LESA-RPI/LESA_OccupancyUnit/Hardware/Enclosure/RenderImages/OSCASSY1.png

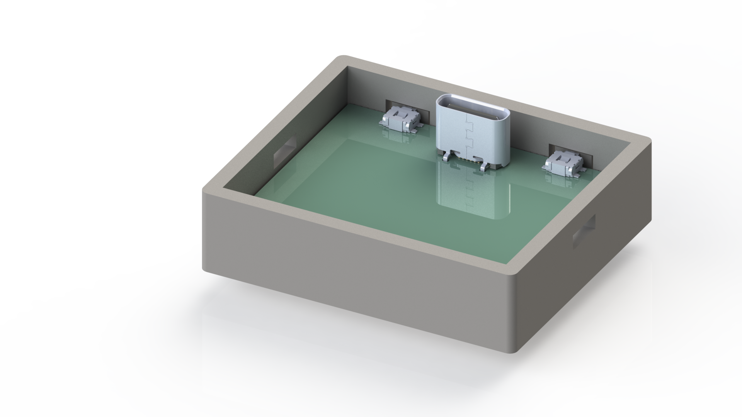
Hardware/Enclosure/RenderImages/OSCASSY1.png
