LESA-RPI/LESA_OccupancyUnit/Hardware/Enclosure/RenderImages/OSCASSY2.png

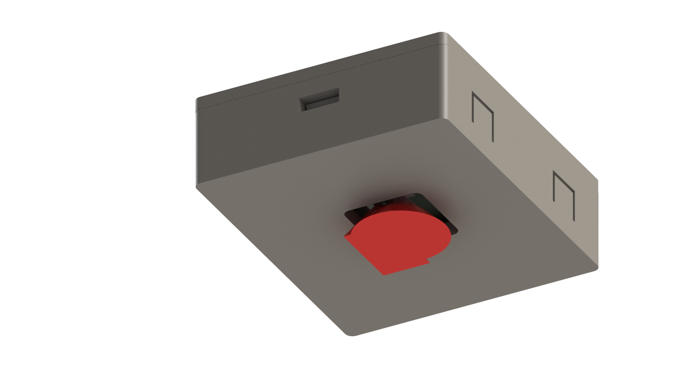
Hardware/Enclosure/RenderImages/OSCASSY2.png
