LESA-RPI/LESA_OccupancyUnit/Hardware/Enclosure/RenderImages/OSCT3view2.png

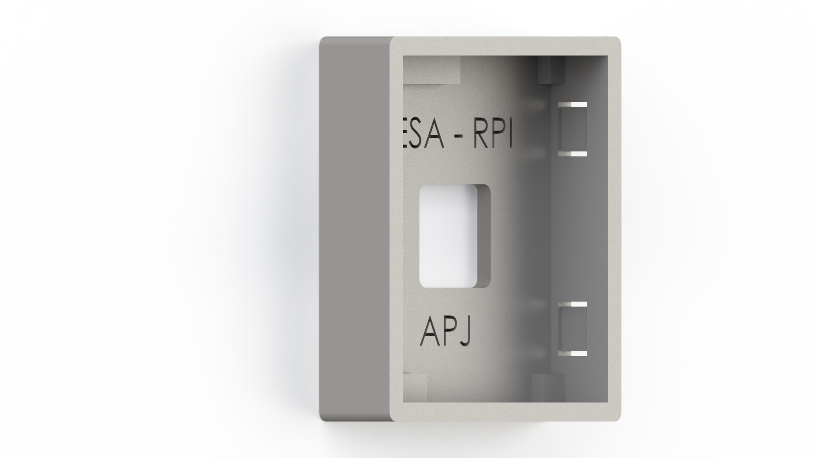
Hardware/Enclosure/RenderImages/OSCT3view2.png
