LESA-RPI/LESA_OccupancyUnit/Hardware/Enclosure/RenderImages/TCS3430.png

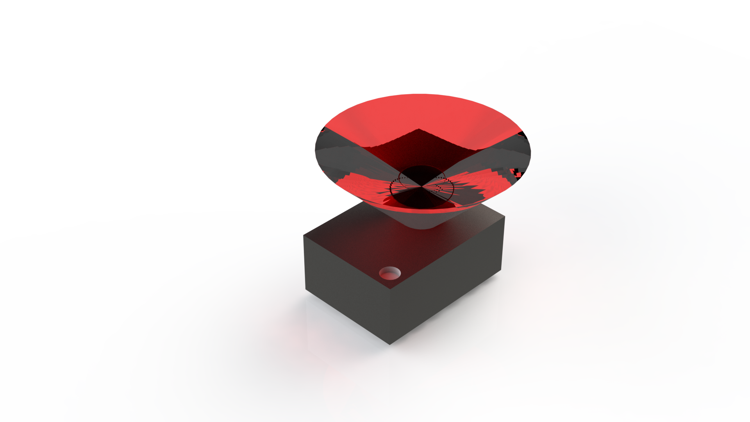
Hardware/Enclosure/RenderImages/TCS3430.png
