LESA-RPI/LESA_OccupancyUnit/Hardware/Enclosure/RenderImages/VL53L8CX.png

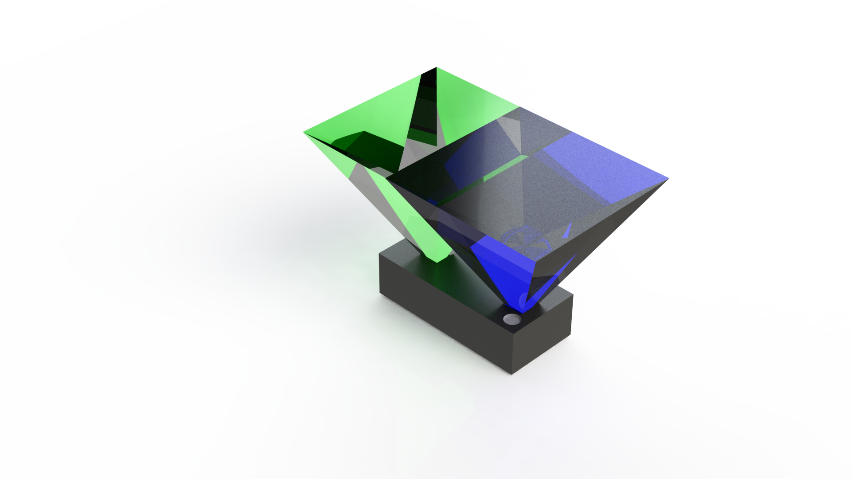
Hardware/Enclosure/RenderImages/VL53L8CX.png
