LESA-RPI/LESA_OccupancyUnit/Hardware/PCBA/-A/Occupancy_Sensor-A/Occupancy_Sensor-A.kicad_sch

## KiCad design Hardware/PCBA/-A/Occupancy_Sensor-A/Occupancy_Sensor-A.kicad_sch (2023-11-09)


Parts:
AE1: Antenna; AN3359_Meander_Antenna
C1, C13, C15, C19: 4.7u; C_0402_1005Metric; Part # CL05A475MP5NRNC
C2, C4, C9, C16, C17, C18, C20, C21, C22: 100n; C_0402_1005Metric; Part # CL05A104KA5NNNC
C3, C5, C6, C7, C8, C10: 1u; C_0402_1005Metric; Part # CL05A105KP5NNNC
C11, C26: 10n; C_0402_1005Metric; Part # CL05B103KB5NNNC
C12, C14: 10p; C_0402_1005Metric; Part # GRM1555C1H100FA01D
C23: 100p; C_0402_1005Metric; Part # GRM1555C1H101JA01D
C24: 0.8p; C_0402_1005Metric; Part # CC0402BRNPO9BNR80
C25: 0.3p; C_0402_1005Metric; Part # GRM1555C1HR30BA01J
C27, C28, C29: C_0402_1005Metric; not fitted
C30: 1.2p; C_0402_1005Metric; Part # CC0402CRNPO9BN1R2
C31: 10n; C_0402_1005Metric; Part # CL05B103KB5NNNC; not fitted
D1: PWR; LED_0603_1608Metric; Part # LTST-C191KRKT
D2: STAT; LED_0603_1608Metric; Part # LTST-C190GKT
J2: Conn_02x05_Odd_Even; PinHeader_2x05_P1.27mm_Vertical_SMD; Part # 20021121-00010C4LF
J3: Conn_Coaxial; CONUFL001-SMD-T; Part # CONUFL001-SMD-T
J4: USB_C_Receptacle; USB4120-03-C; Part # USB4115-03-C
JP1: BATT; SolderJumper-2_P1.3mm_Open_RoundedPad1.0x1.5mm
JP2: USB; SolderJumper-2_P1.3mm_Bridged_RoundedPad1.0x1.5mm
L1: 10u; L_0805_2012Metric; Part # LQM21FN100M70L
L2: 10n; L_0402_1005Metric; Part # LQG15WZ10NJ02D
L3: 2.7n; L_0402_1005Metric; Part # LQG15HS2N7S02D
L4: 0R; R_0603_1608Metric
L5: 3.6n; L_0402_1005Metric; Part # LQG15HS3N6S02
Q1, Q2, Q3, Q4, Q7: BSS138; SOT-23; Part # BSS138
Q6: DMG1012T; SOT-523; Part # DMG1012T-7
R1, R2: 5.1K; R_0402_1005Metric; Part # ERJ-2RKF5101X
R3, R5, R6, R7, R9, R10, R12: 47K; R_0402_1005Metric; Part # ERJ-2RKF4702X
R4, R11: 40.2K; R_0402_1005Metric; Part # RC0402FR-1340K2L
R8, R13, R15, R21: 1K; R_0402_1005Metric; Part # ERJ-2RKF1001X
R14, R16, R17, R18, R19, R20: 2.2K; R_0402_1005Metric; Part # ERJ-2RKF2201X
SW1: BOOT; EVQ-P7A01P; Part # EVQ-P7A01P
SW2: RST; EVQ-P7A01P; Part # EVQ-P7A01P
TP1: 5V; TestPoint_Pad_D2.0mm
TP2: GND; TestPoint_Pad_D2.0mm
TP3: SCL; TestPoint_Pad_D1.0mm
TP4: SDA; TestPoint_Pad_D1.0mm
TP5: INTT; TestPoint_Pad_D1.0mm
TP7: INTC; TestPoint_Pad_D1.0mm
U1: TPS7A0333PDBVR; SOT-23-5; Part # TPS7A0333PDBVR
U2: VL53L8CX; Part # VL53L8CXV0GC/1
U3: ECMF02-2AMX6; ST_UQFN-6L_1.5x1.7mm_P0.5mm; Part # ECMF02-2AMX6
U4: TPS7A0318PDBVR; SOT-23-5; Part # TPS7A0318PDBVR
U5: TCS3430; Part # TCS34303
U6: STM32WB55CGUx; QFN-48-1EP_7x7mm_P0.5mm_EP5.6x5.6mm; Part # STM32WB55CGU6
U8: DEA162450BT-1295A1; Part # DEA162450BT-1295A1
Y2: NX2016SA_32M; Part # CS06465-32M
Y3: NX2012_32K768; Part # MU00797-32.768K

Connections:
1V8_EN: U4.3 (EN), U6.12 (PA3)
+1V8: C2.1, C4.1, C7.1, C8.1, Q1.1 (G), Q2.1 (G), Q3.1 (G), Q4.1 (G), Q7.1 (G), R6.1, R7.1, R14.1, R16.1, R19.1, U2.A3 (IOVDD), U2.B7 (CORE_1V8), U4.5 (OUT), U5.1 (VDD)
+3.3V: C1.1, C5.1, C10.1, C11.1, C13.1, C15.1, C16.1, C17.1, C18.1, C20.1, C22.1, C23.1, J2.1, JP1.1 (A), JP2.1 (A), R9.1, R10.1, R17.1, R18.1, R20.1, R21.1, SW1.2, U1.5 (OUT), U2.C4 (AVDD), U6.8 (VDDA), U6.20 (VDD), U6.23 (VDDRF), U6.34 (VDDSMPS), U6.35 (VDD), U6.48 (VDD)
BOOT: R15.1, SW1.1, U6.4 (PH3)
GND: C1.2, C2.2, C3.2, C4.2, C5.2, C6.2, C7.2, C8.2, C9.2, C10.2, C11.2, C12.1, C13.2, C14.2, C15.2, C16.2, C17.2, C18.2, C19.2, C20.2, C21.2, C22.2, C23.2, C24.2, C25.2, C27.2, C28.2, C29.2, C30.2, D1.1 (K), D2.1 (K), J2.3, J2.5, J2.9, J3.2 (Ext), J4.A1 (GND), J4.A12 (GND), J4.B1 (GND), J4.B12 (GND), Q6.1 (G), R1.2, R2.2, R3.2, R5.2, R12.2, R15.2, SW2.2, TP2.1, U1.2 (GND), U2.A6 (RSVD1), U2.A7 (RSVD2), U2.B4 (PAD), U2.C3 (GND), U2.C6 (RSVD3), U2.C7 (GND), U3.3 (GND), U4.2 (GND), U5.7 (GND), U5.8 (GND), U6.22 (VSSRF), U6.32 (VSSSMPS), U6.49 (VSS), U8.2 (GND), U8.4 (GND), Y2.2, Y2.4
I2C_RST: R4.1, U6.17 (PA8)
I2C_RST_1V8: R4.2, R5.1, U2.C2 (NCS)
INT_CLR_1V8: Q3.2 (S), R14.2, U5.4 (INT)
INT_CLR_3V3: Q3.3 (D), R17.2, TP7.1, U6.42 (PA15)
INT_TOF_1V8: Q1.2 (S), R6.2, U2.A1 (INT)
INT_TOF_3V3: Q1.3 (D), R9.2, TP5.1, U6.15 (PA6)
LPn_1V8: R11.2, R12.1, U2.A2 (LPn)
LPn_3V3: R11.1, U6.14 (PA5)
NRST: C9.1, J2.10, R21.2, SW2.1, U6.7 (NRST)
unnamed: AE1.1, C30.1, L5.2
unnamed: C19.1, L1.1, U6.31 (VFBSMPS)
unnamed: C21.1, JP2.2 (B), U6.40 (VDDUSB)
unnamed: C25.1, L3.2, U8.1
unnamed: C26.1, C31.1, U8.3
unnamed: C26.2, C29.1, L5.1
unnamed: C27.1, J3.1 (In), L4.2
unnamed: C28.1, C31.2, L4.1
unnamed: D1.2 (A), R8.1
unnamed: D2.2 (A), R13.1
unnamed: J4.A5 (CC1), R1.1
unnamed: J4.A6 (D+), J4.B6 (D+), U3.1 (D+_in)
unnamed: J4.A7 (D-), J4.B7 (D-), U3.2 (D-_in)
unnamed: J4.B5 (CC2), R2.1
unnamed: JP1.2 (B), U6.1 (VBAT)
unnamed: L1.2, L2.1
unnamed: L2.2, U6.33 (VLXSMPS)
unnamed: Q6.2 (S), TP1.1
unnamed: R3.1, U2.C1 (SPI_I2C_N)
OSC32_IN: C14.1, U6.2 (PC14), Y3.2
OSC32_OUT: C12.2, U6.3 (PC15), Y3.1
OSC_IN: U6.25 (OSC_IN), Y2.3
OSC_OUT: U6.24 (OSC_OUT), Y2.1
PB5: R13.2, U6.45 (PB5)
RF: C24.1, L3.1, U6.21 (RF1)
SCL_1V8: Q4.2 (S), R16.2, U2.A5 (SCL/MCLK), U5.3 (SCL)
SCL_3V3: Q4.3 (D), R18.2, TP3.1, U6.46 (PB6)
SDA_1V8: Q7.2 (S), R19.2, U2.A4 (SDA/MOSI), U5.2 (SDA)
SDA_3V3: Q7.3 (D), R20.2, TP4.1, U6.47 (PB7)
SWCLK: J2.4, U6.41 (PA14)
SWDIO: J2.2, U6.39 (PA13)
SWO: J2.6, U6.43 (PB3)
SYNC_1V8: Q2.2 (S), R7.2, U2.B1 (SYNC)
SYNC_3V3: Q2.3 (D), R10.2, U6.16 (PA7)
USB_N: U3.5 (D-_out), U6.37 (PA11)
USB_P: U3.6 (D+_out), U6.38 (PA12)
VBUS: C3.1, C6.1, J4.A4 (VBUS), J4.A9 (VBUS), J4.B4 (VBUS), J4.B9 (VBUS), Q6.3 (D), R8.2, U1.1 (IN), U1.3 (EN), U4.1 (IN)

Notes on the sheet:
USB
STATUS LED
TCS340 COLOR SENSOR
Depop FET and 3V3-side pullup if SYNC not used
VL53L8 TOF SENSOR
BOOT SELECTOR
Microcontroller Flash/Ram Code: STM32WB55CxU6 Where x is: C = 256Kb E = 512Kb G = 1024Kb Consider using a lower memory microcontroller if firmware not utilizing excess flash.
REGULATORS
Antenna Band Filter
SWD HEADER
I2C Reset active high Voltage divider ensures 1.8V and required 47K pulldown
RESET SWITCH
MICROCONTROLLER
