LESA-RPI/LESA_OccupancyUnit/Core/Inc/main.h

#define B1_Pin GPIO_PIN_4
#define B1_GPIO_Port GPIOC
#define LD2_Pin GPIO_PIN_0
#define LD2_GPIO_Port GPIOB
#define LD3_Pin GPIO_PIN_1
#define LD3_GPIO_Port GPIOB
#define JTMS_Pin GPIO_PIN_13
#define JTMS_GPIO_Port GPIOA
#define JTCK_Pin GPIO_PIN_14
#define JTCK_GPIO_Port GPIOA
#define B2_Pin GPIO_PIN_0
#define B2_GPIO_Port GPIOD
#define B3_Pin GPIO_PIN_1
#define B3_GPIO_Port GPIOD
#define C_Pin GPIO_PIN_2
#define C_GPIO_Port GPIOC
#define JTDO_Pin GPIO_PIN_3
#define JTDO_GPIO_Port GPIOB
#define LD1_Pin GPIO_PIN_5
#define LD1_GPIO_Port GPIOB
#define STLINK_RX_Pin GPIO_PIN_6
#define STLINK_RX_GPIO_Port GPIOB
#define STLINK_TX_Pin GPIO_PIN_7
#define STLINK_TX_GPIO_Port GPIOB
