LESA-RPI/LESA_OccupancyUnit/CG_chip_ioc/Occ_sensor/Core/Inc/custom_ranging_sensor.h

/**
  ******************************************************************************
  * @file    custom_ranging_sensor.h
  * @author  IMG SW Application Team
  * @brief   This file contains definitions for the BSP Ranging Sensors
  *          interface for custom boards
  ******************************************************************************
  * @attention
  *
  * Copyright (c) 2022 STMicroelectronics.
  * All rights reserved.
  *
  * This software is licensed under terms that can be found in the LICENSE file
  * in the root directory of this software component.
  * If no LICENSE file comes with this software, it is provided AS-IS.
  *
  ******************************************************************************
  */

/* Define to prevent recursive inclusion -------------------------------------*/
#ifndef __CUSTOM_RANGING_SENSOR_H__
#define __CUSTOM_RANGING_SENSOR_H__

#ifdef __cplusplus
 extern "C" {
#endif

/* Includes ------------------------------------------------------------------*/

#include "custom_tof_conf.h"
#include "ranging_sensor.h"

#ifndef USE_CUSTOM_RANGING_VL53L8CX
#define USE_CUSTOM_RANGING_VL53L8CX (1U)
#endif

#if (USE_CUSTOM_RANGING_VL53L8CX == 1U)
#include "vl53l8cx.h"
#endif

#if (USE_CUSTOM_RANGING_VL53L8CX == 1U)
#define CUSTOM_VL53L8CX (0)
#endif

#define RANGING_SENSOR_VL53L8CX_ADDRESS     (VL53L8CX_DEVICE_ADDRESS)
#define RANGING_SENSOR_NB_TARGET_PER_ZONE   (VL53L8CX_NB_TARGET_PER_ZONE)
#define RANGING_SENSOR_MAX_NB_ZONES         (VL53L8CX_MAX_NB_ZONES)

#define RS_PROFILE_4x4_CONTINUOUS          (VL53L8CX_PROFILE_4x4_CONTINUOUS)
#define RS_PROFILE_4x4_AUTONOMOUS          (VL53L8CX_PROFILE_4x4_AUTONOMOUS)
#define RS_PROFILE_8x8_CONTINUOUS          (VL53L8CX_PROFILE_8x8_CONTINUOUS)
#define RS_PROFILE_8x8_AUTONOMOUS          (VL53L8CX_PROFILE_8x8_AUTONOMOUS)

#define RS_IT_DEFAULT        (VL53L8CX_IT_DEFAULT)       /*!< IT if new measurement is ready (no thresholds) */
#define RS_IT_IN_WINDOW      (VL53L8CX_IT_IN_WINDOW)     /*!< IT if distance > thresh_high */
#define RS_IT_OUT_OF_WINDOW  (VL53L8CX_IT_OUT_OF_WINDOW) /*!< IT if distance < LowThreshold OR distance > HighThreshold */
#define RS_IT_BELOW_LOW      (VL53L8CX_IT_BELOW_LOW)     /*!< IT if distance <= LowThreshold */
#define RS_IT_ABOVE_HIGH     (VL53L8CX_IT_ABOVE_HIGH)    /*!< IT if distance > HighThreshold */
#define RS_IT_EQUAL_LOW      (VL53L8CX_IT_EQUAL_LOW)     /*!< IT if distance == LowThreshold */
#define RS_IT_NOT_EQUAL_LOW  (VL53L8CX_IT_NOT_EQUAL_LOW) /*!< IT if distance != LowThreshold */

#define RS_MODE_BLOCKING_CONTINUOUS        (VL53L8CX_MODE_BLOCKING_CONTINUOUS)
#define RS_MODE_BLOCKING_ONESHOT           (VL53L8CX_MODE_BLOCKING_ONESHOT)
#define RS_MODE_ASYNC_CONTINUOUS           (VL53L8CX_MODE_ASYNC_CONTINUOUS)
#define RS_MODE_ASYNC_ONESHOT              (VL53L8CX_MODE_ASYNC_ONESHOT)

#define CUSTOM_RANGING_INSTANCES_NBR    (USE_CUSTOM_RANGING_VL53L8CX)

#define CUSTOM_RANGING_POWERMODE_ON   	(0U)  /*!< run */
#define CUSTOM_RANGING_POWERMODE_OFF  	(1U)  /*!< standby */

#if (CUSTOM_RANGING_INSTANCES_NBR == 0U)
#error "No ranging sensor instance has been selected"
#endif

typedef struct
{
  uint32_t NumberOfZones;
  uint32_t MaxNumberOfTargetsPerZone;
  uint32_t CustomROI;          /*!< Not available: 0, Available: 1 */
  uint32_t ThresholdDetection; /*!< Not available: 0, Available: 1 */
} RANGING_SENSOR_Capabilities_t;

typedef struct
{
  uint32_t RangingProfile;
  uint32_t TimingBudget;   /*!< Expressed in milliseconds */
  uint32_t Frequency;      /*!< Expressed in Hz */
  uint32_t EnableAmbient;  /*<! Enable: 1, Disable: 0 */
  uint32_t EnableSignal;   /*<! Enable: 1, Disable: 0 */
} RANGING_SENSOR_ProfileConfig_t;

typedef struct
{
  uint8_t TopLeftX;   /*!< Top Left x coordinate */
  uint8_t TopLeftY;   /*!< Top Left y coordinate */
  uint8_t BotRightX;  /*!< Bot Right x coordinate */
  uint8_t BotRightY;  /*!< Bot Right y coordinate */
} RANGING_SENSOR_ROIConfig_t;

typedef struct
{
  uint32_t Criteria;
  uint32_t LowThreshold;
  uint32_t HighThreshold;
} RANGING_SENSOR_ITConfig_t;

typedef struct
{
  uint32_t NumberOfTargets;
  uint32_t Distance[RANGING_SENSOR_NB_TARGET_PER_ZONE];  /*!< millimeters */
  uint32_t Status[RANGING_SENSOR_NB_TARGET_PER_ZONE];    /*!< OK: 0, NOK: !0 */
  float_t Ambient[RANGING_SENSOR_NB_TARGET_PER_ZONE];    /*!< kcps / spad */
  float_t Signal[RANGING_SENSOR_NB_TARGET_PER_ZONE];     /*!< kcps / spad */
} RANGING_SENSOR_ZoneResult_t;

typedef struct
{
  uint32_t NumberOfZones;
  RANGING_SENSOR_ZoneResult_t ZoneResult[RANGING_SENSOR_MAX_NB_ZONES];
} RANGING_SENSOR_Result_t;

extern void *CUSTOM_RANGING_CompObj[CUSTOM_RANGING_INSTANCES_NBR];

int32_t CUSTOM_RANGING_SENSOR_Init(uint32_t Instance);
int32_t CUSTOM_RANGING_SENSOR_DeInit(uint32_t Instance);
int32_t CUSTOM_RANGING_SENSOR_ReadID(uint32_t Instance, uint32_t *pId);
int32_t CUSTOM_RANGING_SENSOR_GetCapabilities(uint32_t Instance, RANGING_SENSOR_Capabilities_t *pCapabilities);
int32_t CUSTOM_RANGING_SENSOR_ConfigProfile(uint32_t Instance, RANGING_SENSOR_ProfileConfig_t *pConfig);
int32_t CUSTOM_RANGING_SENSOR_ConfigROI(uint32_t Instance, RANGING_SENSOR_ROIConfig_t *pConfig);
int32_t CUSTOM_RANGING_SENSOR_ConfigIT(uint32_t Instance, RANGING_SENSOR_ITConfig_t *pConfig);
int32_t CUSTOM_RANGING_SENSOR_GetDistance(uint32_t Instance, RANGING_SENSOR_Result_t *pResult);
int32_t CUSTOM_RANGING_SENSOR_Start(uint32_t Instance, uint8_t Mode);
int32_t CUSTOM_RANGING_SENSOR_Stop(uint32_t Instance);
int32_t CUSTOM_RANGING_SENSOR_SetAddress(uint32_t Instance, uint16_t Address);
int32_t CUSTOM_RANGING_SENSOR_GetAddress(uint32_t Instance, uint16_t *pAddress);
int32_t CUSTOM_RANGING_SENSOR_SetPowerMode(uint32_t Instance, uint32_t PowerMode);
int32_t CUSTOM_RANGING_SENSOR_GetPowerMode(uint32_t Instance, uint32_t *pPowerMode);

#ifdef __cplusplus
}
#endif

#endif /* __CUSTOM_RANGING_SENSOR_H__ */
