LESA-RPI/LESA_OccupancyUnit/Core/Src/stm32wbxx_it.c

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

/* Includes ------------------------------------------------------------------*/
#include "main.h"
#include "stm32wbxx_it.h"
/* USER CODE BEGIN Includes */
#include "appli_mesh.h"
#include "PWM_handlers.h"
/* USER CODE END Includes */

/* External variables --------------------------------------------------------*/
extern IPCC_HandleTypeDef hipcc;
extern DMA_HandleTypeDef hdma_lpuart1_tx;
extern DMA_HandleTypeDef hdma_usart1_tx;
extern TIM_HandleTypeDef htim1;
extern TIM_HandleTypeDef htim2;
extern UART_HandleTypeDef hlpuart1;
extern UART_HandleTypeDef huart1;
extern RTC_HandleTypeDef hrtc;
/******************************************************************************/
/*           Cortex Processor Interruption and Exception Handlers          */
/******************************************************************************/
/**
  * @brief This function handles Non maskable interrupt.
 */
void NMI_Handler(void)
{
}

/**
  * @brief This function handles Hard fault interrupt.
 */
void HardFault_Handler(void)
{
  /* USER CODE BEGIN HardFault_IRQn 0 */
  BSP_LED_On(LED_RED);
#ifndef DISABLE_TRACES
  printf("HARDFAULT !\r\n");
#endif
  /* USER CODE END HardFault_IRQn 0 */
  while (1)
  {
  }
}

/**
  * @brief This function handles Memory management fault.
  */
void MemManage_Handler(void)
{
  while (1)
  {
  }
}

/**
  * @brief This function handles Prefetch fault, memory access fault.
  */
void BusFault_Handler(void)
{
  while (1)
  {
  }
}

/**
  * @brief This function handles Undefined instruction or illegal state.
  */
void UsageFault_Handler(void)
{
  while (1)
  {
  }
}

/**
  * @brief This function handles System service call via SWI instruction.
 */
void SVC_Handler(void)
{
}

/**
  * @brief This function handles Debug monitor.
 */
void DebugMon_Handler(void)
{
}

/**
  * @brief This function handles Pendable request for system service.
 */
void PendSV_Handler(void)
{
}

/**
  * @brief This function handles System tick timer.
 */
void SysTick_Handler(void)
{
  HAL_IncTick();
}

/******************************************************************************/
/* STM32WBxx Peripheral Interrupt Handlers                                    */
/* Add here the Interrupt Handlers for the used peripherals.                  */
/* For the available peripheral interrupt handler names,                      */
/* please refer to the startup file (startup_stm32wbxx.s).                    */
/******************************************************************************/

/**
  * @brief This function handles RTC wake-up interrupt through EXTI line 19.
  */
void RTC_WKUP_IRQHandler(void)
{
  HAL_RTCEx_WakeUpTimerIRQHandler(&hrtc);
}

/**
  * @brief This function handles DMA1 channel4 global interrupt.
  */
void DMA1_Channel4_IRQHandler(void)
{
  HAL_DMA_IRQHandler(&hdma_lpuart1_tx);
}

/**
  * @brief This function handles USART1 global interrupt.
  */
void USART1_IRQHandler(void)
{
  HAL_UART_IRQHandler(&huart1);
}

/**
  * @brief This function handles LPUART1 global interrupt.
  */
void LPUART1_IRQHandler(void)
{
  HAL_UART_IRQHandler(&hlpuart1);
}

/**
  * @brief This function handles IPCC RX occupied interrupt.
  */
void IPCC_C1_RX_IRQHandler(void)
{
  HAL_IPCC_RX_IRQHandler(&hipcc);
}

/**
  * @brief This function handles IPCC TX free interrupt.
  */
void IPCC_C1_TX_IRQHandler(void)
{
  HAL_IPCC_TX_IRQHandler(&hipcc);
}

/**
  * @brief This function handles HSEM global interrupt.
  */
void HSEM_IRQHandler(void)
{
  HAL_HSEM_IRQHandler();
}

/**
  * @brief This function handles DMA2 channel4 global interrupt.
  */
void DMA2_Channel4_IRQHandler(void)
{
  HAL_DMA_IRQHandler(&hdma_usart1_tx);
}

/* USER CODE BEGIN 1 */
/**
 * @brief  This function handles External line
 *         interrupt request.
 * @param  None
 * @retval None
 */
void PUSH_BUTTON_SW1_EXTI_IRQHandler(void)
{
  HAL_GPIO_EXTI_IRQHandler(BUTTON_SW1_PIN);
}

/**
 * @brief  This function handles External line
 *         interrupt request.
 * @param  None
 * @retval None
 */
void PUSH_BUTTON_SW2_EXTI_IRQHandler(void)
{
  HAL_GPIO_EXTI_IRQHandler(BUTTON_SW2_PIN);
}

/**
 * @brief  This function handles External line
 *         interrupt request.
 * @param  None
 * @retval None
 */
void PUSH_BUTTON_SW3_EXTI_IRQHandler(void)
{
  HAL_GPIO_EXTI_IRQHandler(BUTTON_SW3_PIN);
}

/**
 * @brief  This function handles External line
 *         interrupt request.
 * @param  None
 * @retval None
 */
void COLOR_INT_EXTI_IRQHandler(void)
{
  HAL_GPIO_EXTI_IRQHandler(COLOR_INT_PIN);
}

#ifdef SAVE_MODEL_STATE_POWER_FAILURE_DETECTION       
/**
 * @brief  This function handles External line
 *         interrupt request.
 * @param  None
 * @retval None
 */
void POWEROFF_EXTI_IRQHandler(void)
{
  HAL_GPIO_EXTI_IRQHandler(POWEROFF_PIN);
}
#endif

#if 0
/**
  * @brief This function handles TIM2 global interrupt.
  */
void TIM2_IRQHandler(void)
{
  HAL_TIM_IRQHandler(&htim2);
}

/**
  * @brief This function handles TIM1 global interrupt.
  */
void TIM1_CC_IRQHandler(void)
{
  HAL_TIM_IRQHandler(&htim1);
}
#endif

/* USER CODE END 1 */
